himikat123/Big_Clock_BIM32/Solidworks_2023/bed/bed_cover_middle.png

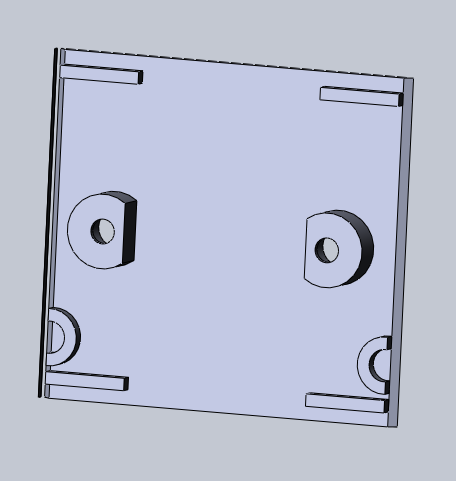
Solidworks_2023/bed/bed_cover_middle.png
