himikat123/Big_Clock_BIM32/Solidworks_2023/buttons/buttons.png

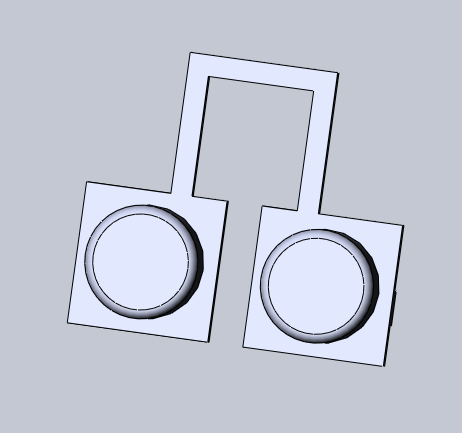
Solidworks_2023/buttons/buttons.png
