himikat123/Big_Clock_BIM32/Solidworks_2023/digit/digit_cover.png

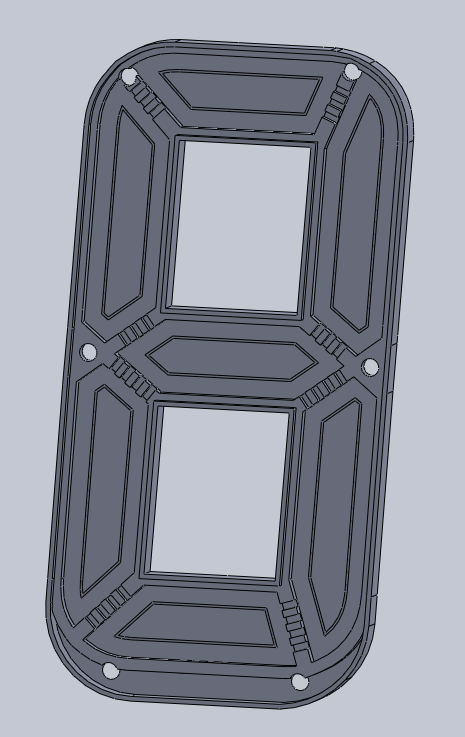
Solidworks_2023/digit/digit_cover.png
