himikat123/Big_Clock_BIM32/Solidworks_2023/digit/digit_frame.png

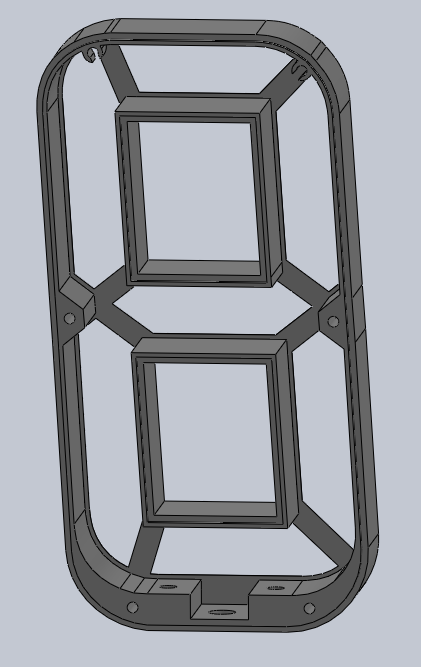
Solidworks_2023/digit/digit_frame.png
