himikat123/Big_Clock_BIM32/Solidworks_2023/jumpers/jumper_2.png

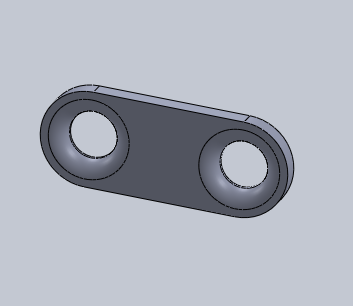
Solidworks_2023/jumpers/jumper_2.png
