himikat123/Big_Clock_BIM32/Solidworks_2023/jumpers/jumper_3.png

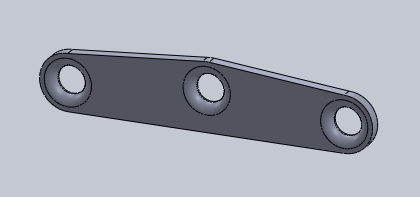
Solidworks_2023/jumpers/jumper_3.png
