himikat123/Big_Clock_BIM32/Solidworks_2023/points/points_diffuser.png

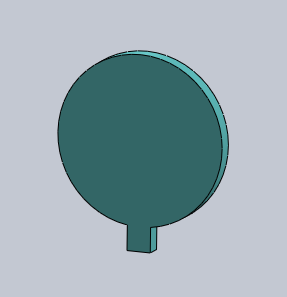
Solidworks_2023/points/points_diffuser.png
