himikat123/Big_Clock_BIM32/Solidworks_2023/points/points_reflector.png

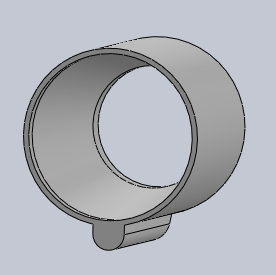
Solidworks_2023/points/points_reflector.png
