himikat123/Big_Clock_BIM32/STL/bed/bed_cover_2.png

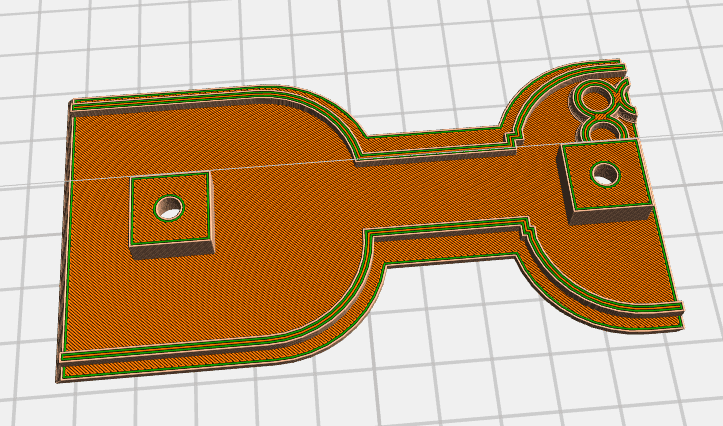
STL/bed/bed_cover_2.png
