himikat123/Big_Clock_BIM32/STL/bed/bed_left.png

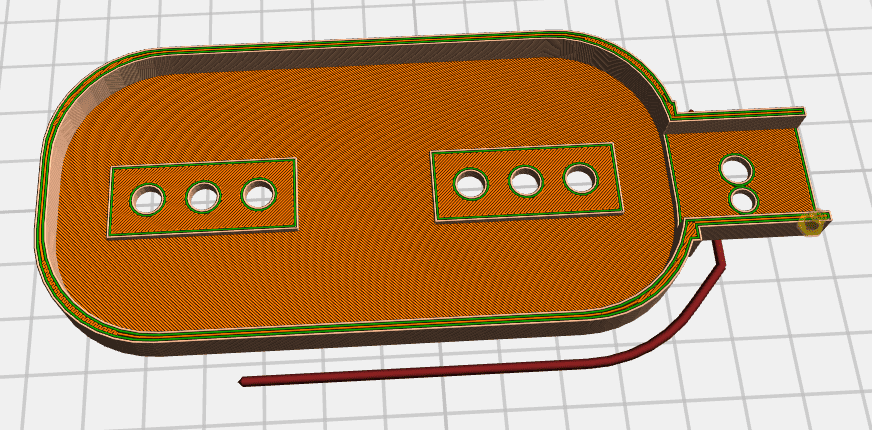
STL/bed/bed_left.png
