himikat123/Big_Clock_BIM32/STL/bed/bed_middle.png

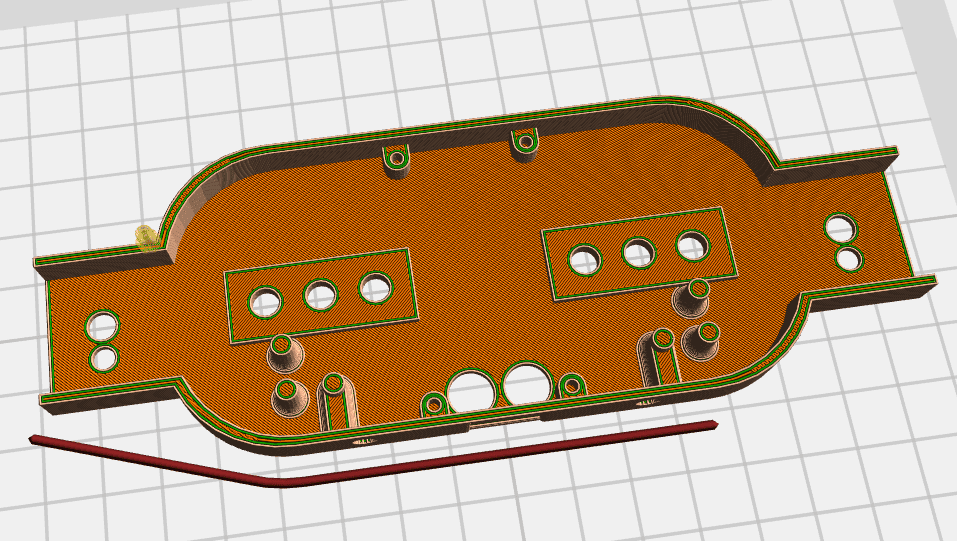
STL/bed/bed_middle.png
