himikat123/Big_Clock_BIM32/STL/bed/bed_right.png

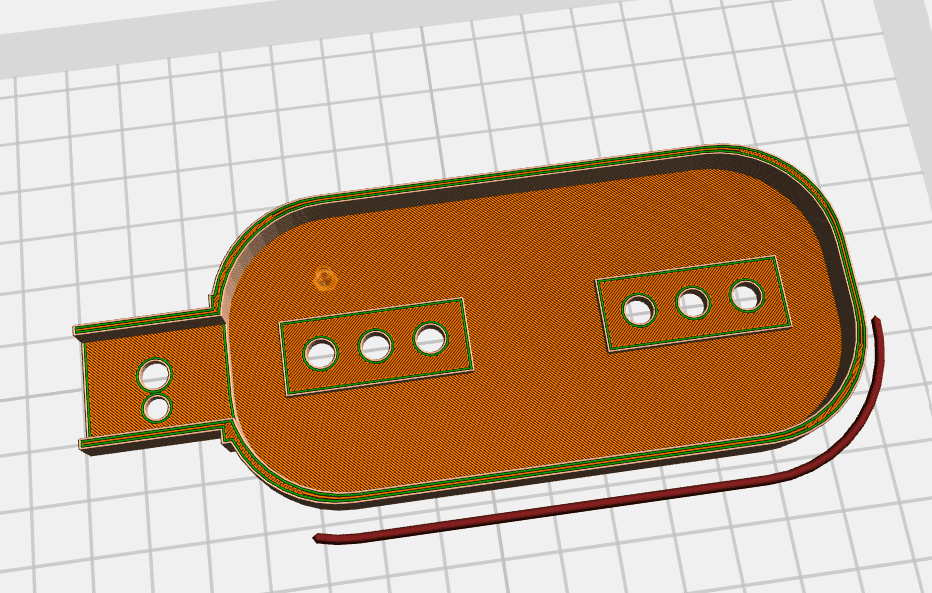
STL/bed/bed_right.png
