himikat123/Big_Clock_BIM32/STL/buttons/buttons.png

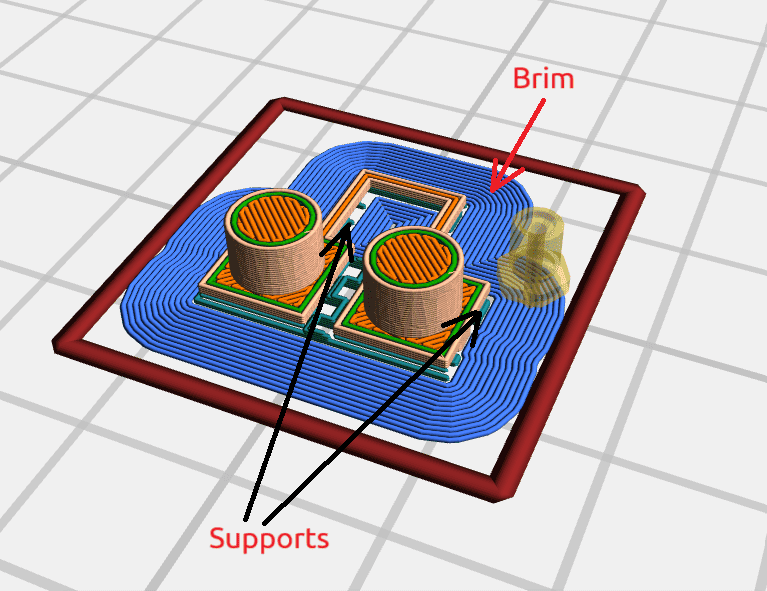
STL/buttons/buttons.png
