himikat123/Big_Clock_BIM32/STL/digit/digit_cover.png

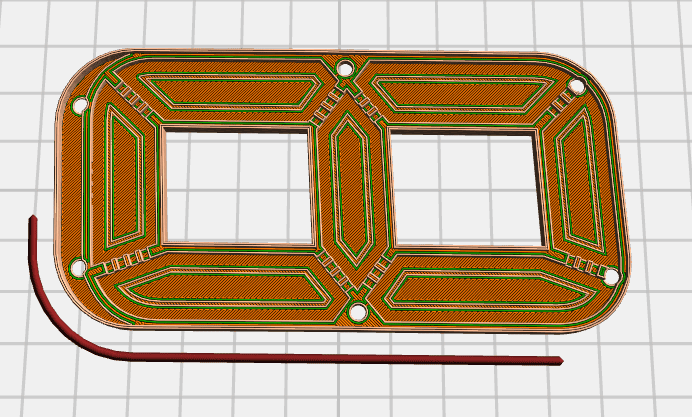
STL/digit/digit_cover.png
