himikat123/Big_Clock_BIM32/STL/digit/digit_diffuser.png

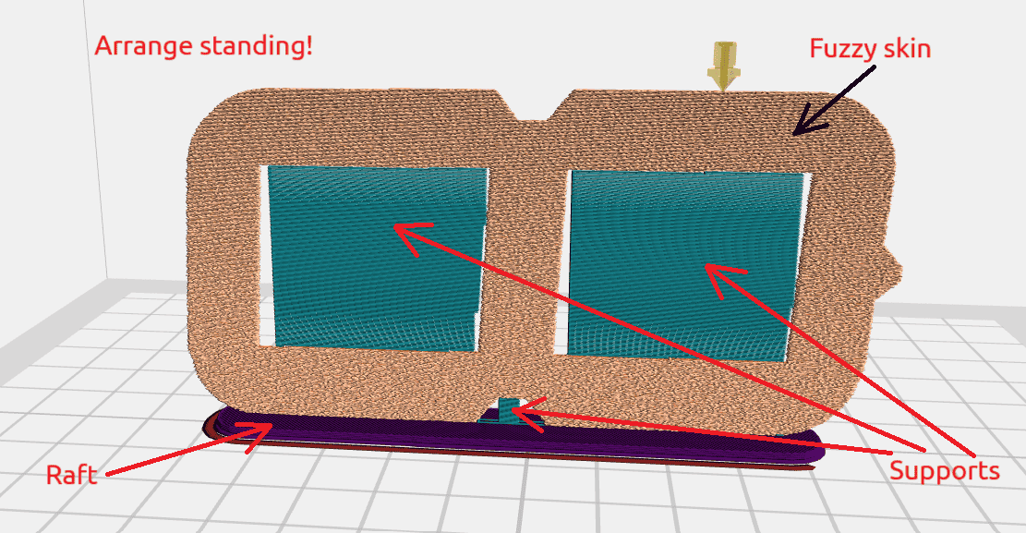
STL/digit/digit_diffuser.png
