himikat123/Big_Clock_BIM32/STL/digit/digit_frame.png

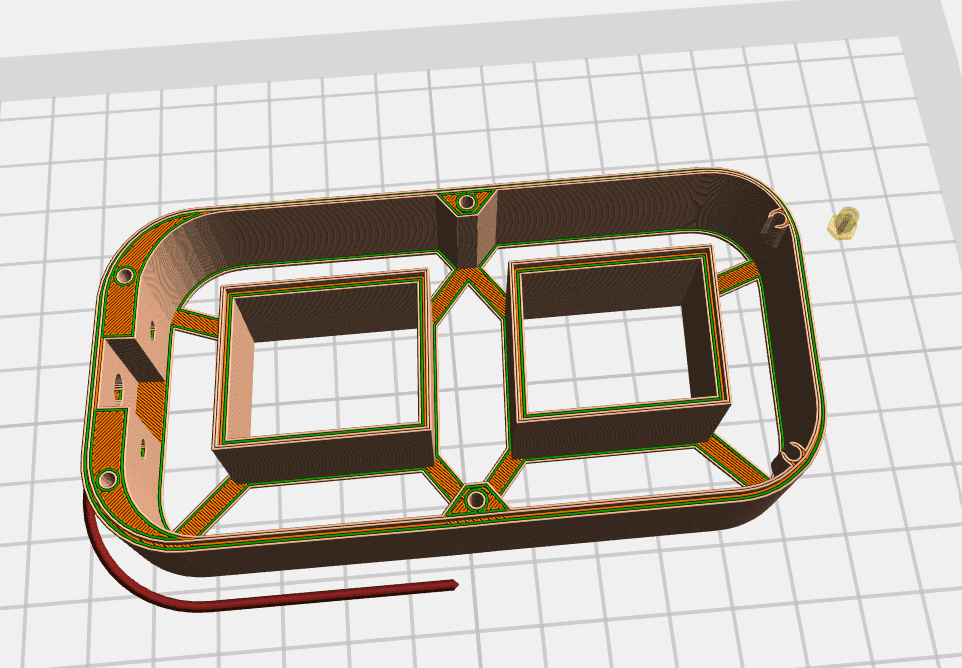
STL/digit/digit_frame.png
