himikat123/Big_Clock_BIM32/STL/digit/digit_reflector.png

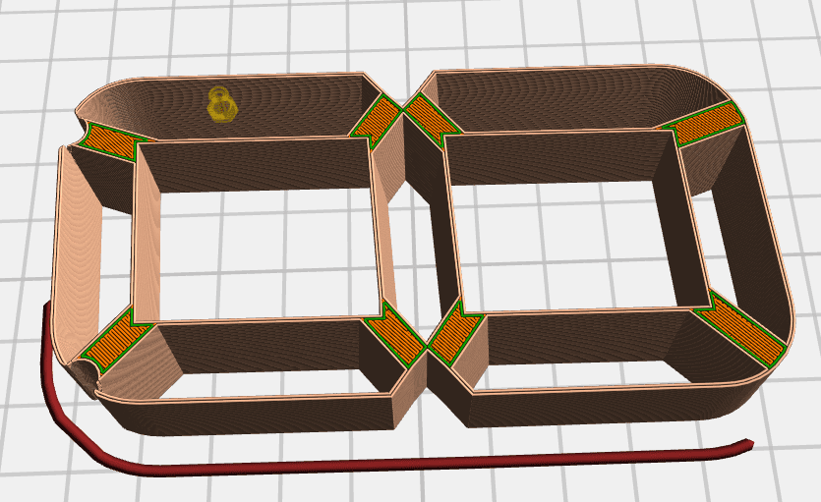
STL/digit/digit_reflector.png
