himikat123/Big_Clock_BIM32/STL/jumpers/jumper_3.png

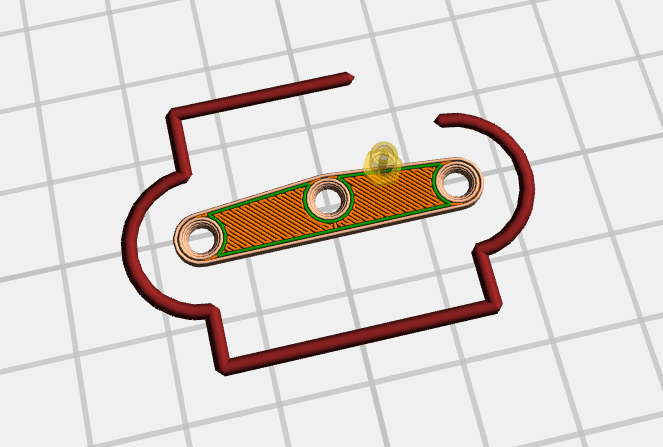
STL/jumpers/jumper_3.png
