himikat123/Big_Clock_BIM32/STL/points/points_cover.png

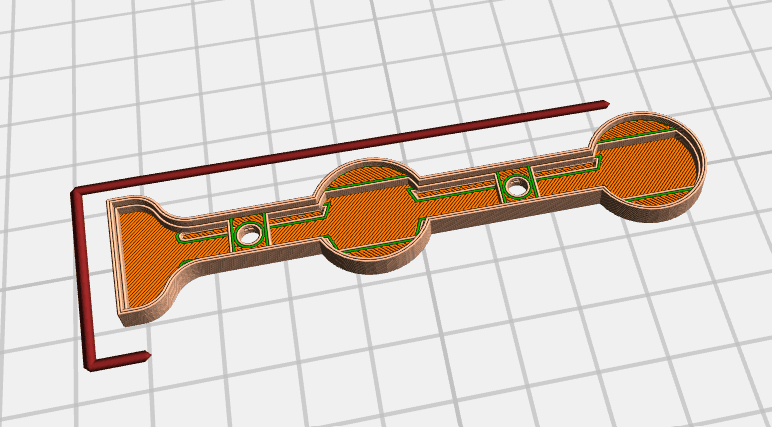
STL/points/points_cover.png
