himikat123/Big_Clock_BIM32/STL/points/points_frame.png

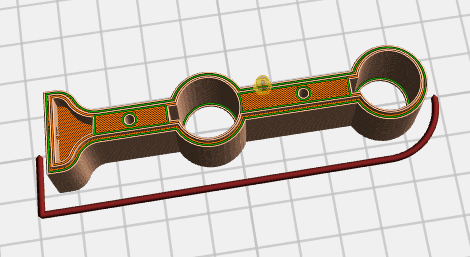
STL/points/points_frame.png
