himikat123/Big_Clock_BIM32/STL/points/points_reflector.png

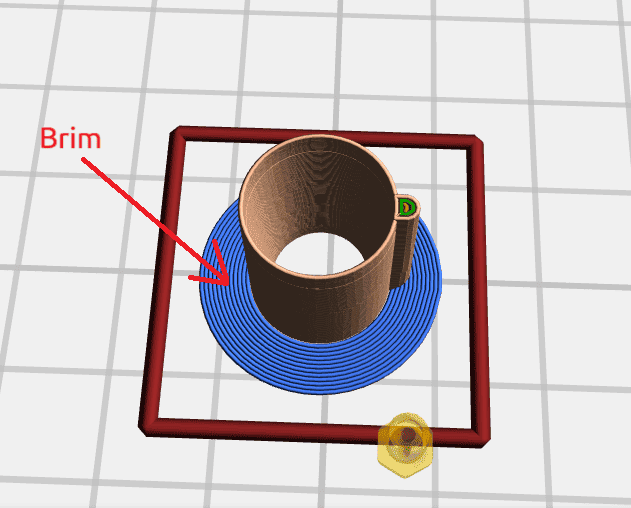
STL/points/points_reflector.png
