himikat123/Big_Clock_BIM32/Solidworks_2023/asssembly.SLDASM

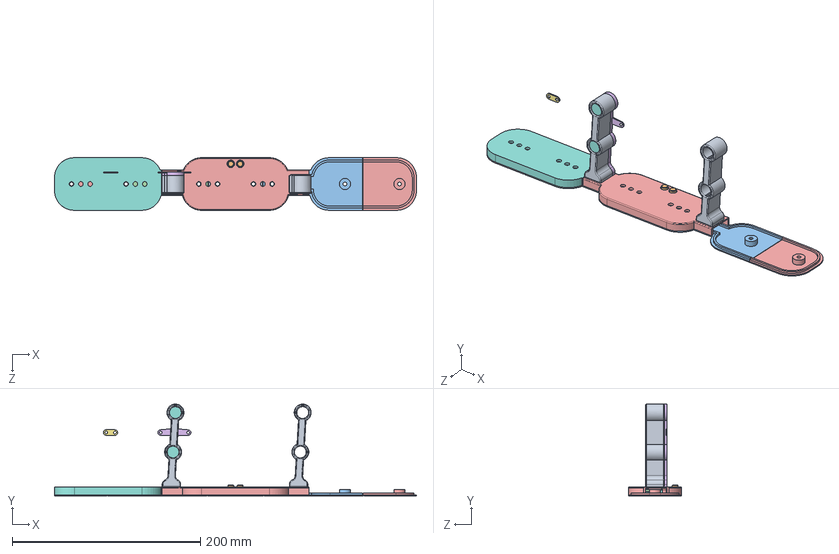
[picture p58: CAD file, 2024-10-17]
Solidworks_2023/asssembly.SLDASM
384.8 x 97.7 x 56.0 mm
points_frame x 2
points_diffuser x 2
points_reflector
points_cover
bed_middle
esp2
btn1 x 2
btn2 x 2
usb
bed_left
jumper_2
jumper_3
bed_cover_edge x 2
bed_cover_2
bed_cover_3
buttons
bed_cover_middle
