himikat123/Big_Clock_BIM32/STL/points/points_reflector.STL

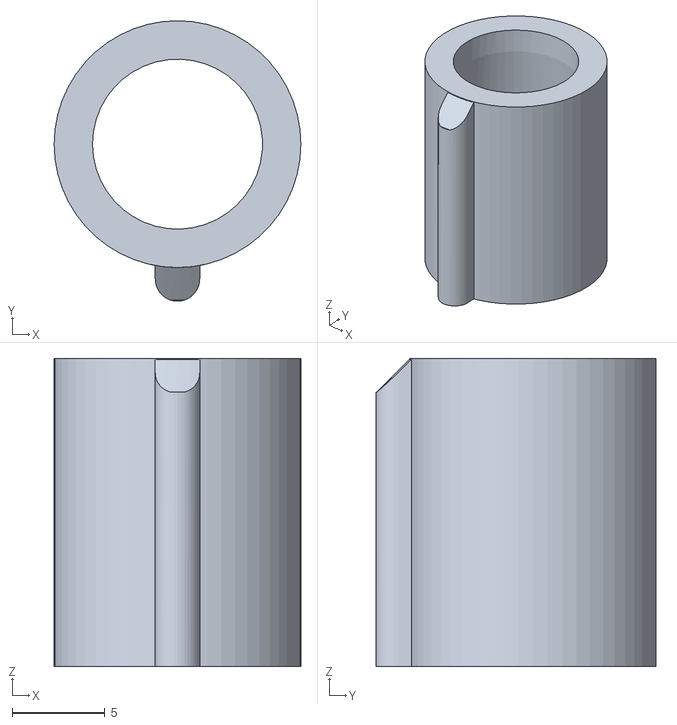
[picture p73: CAD file, 2024-10-17]
STL/points/points_reflector.STL
13.3 x 15.1 x 16.6
