himikat123/Big_Clock_BIM32/Solidworks_2023/bed/bed_cover_middle.SLDPRT

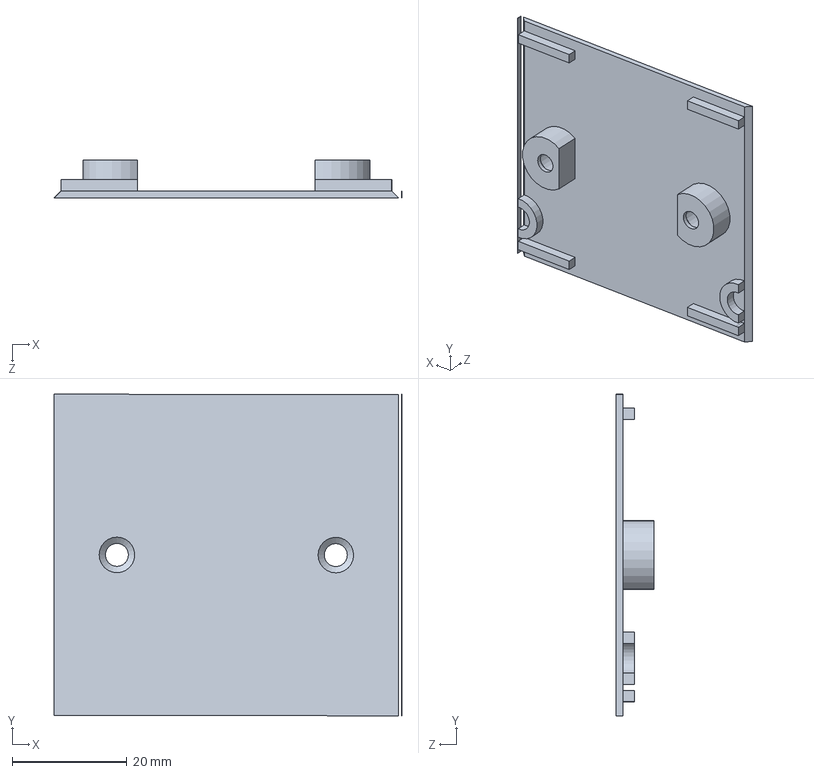
[picture p74: CAD file, 2024-10-17]
Solidworks_2023/bed/bed_cover_middle.SLDPRT
60.6 x 56.0 x 6.60 mm
