himikat123/Big_Clock_BIM32/Solidworks_2023/digit/reflector/G_ref.SLDPRT

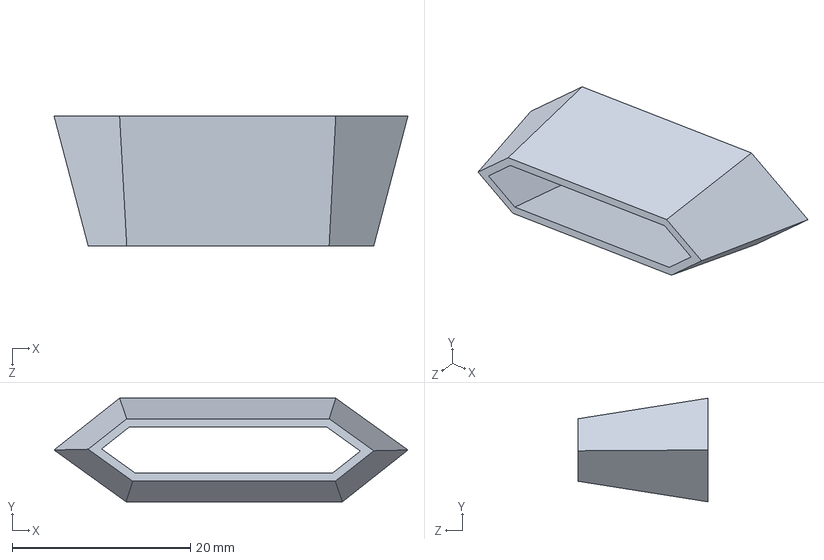
[picture p75: CAD file, 2026-07-15]
Solidworks_2023/digit/reflector/G_ref.SLDPRT
39.7 x 11.6 x 14.6 mm
