himikat123/Big_Clock_BIM32/Solidworks_2023/node mcu/esp2.SLDPRT

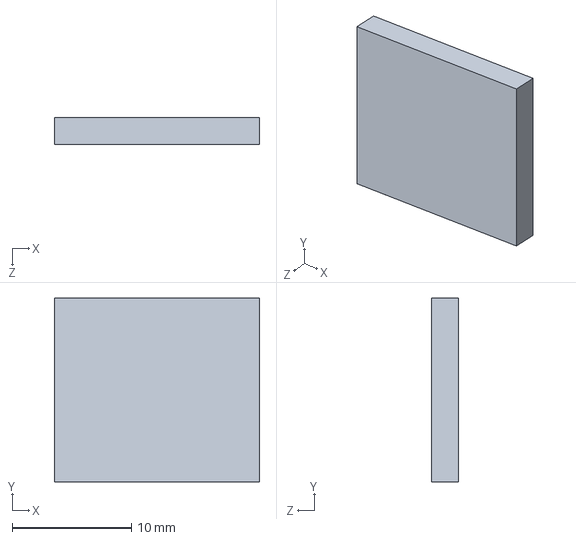
[picture p76: CAD file, 2024-10-17]
Solidworks_2023/node mcu/esp2.SLDPRT
17.2 x 15.4 x 2.30 mm
