himikat123/Big_Clock_BIM32/Solidworks_2023/pcb/pcbPoints.step

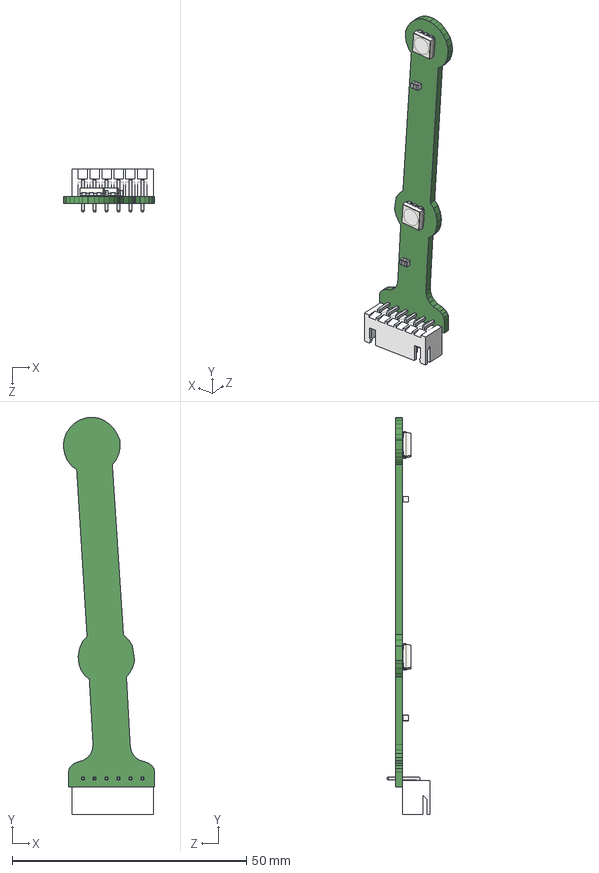
[picture p77: CAD file, 2026-05-27]
Solidworks_2023/pcb/pcbPoints.step
19.5 x 84.7 x 9.22 mm
Board_pcbPoints
0805B104M500NT x 2
led_plcc6_5050_metric x 2
JST_-_XH_-_Thru_(R)_-_6Pin_-_2.54mm
