himikat123/Big_Clock_BIM32/Solidworks_2023/points/points_diffuser.SLDPRT

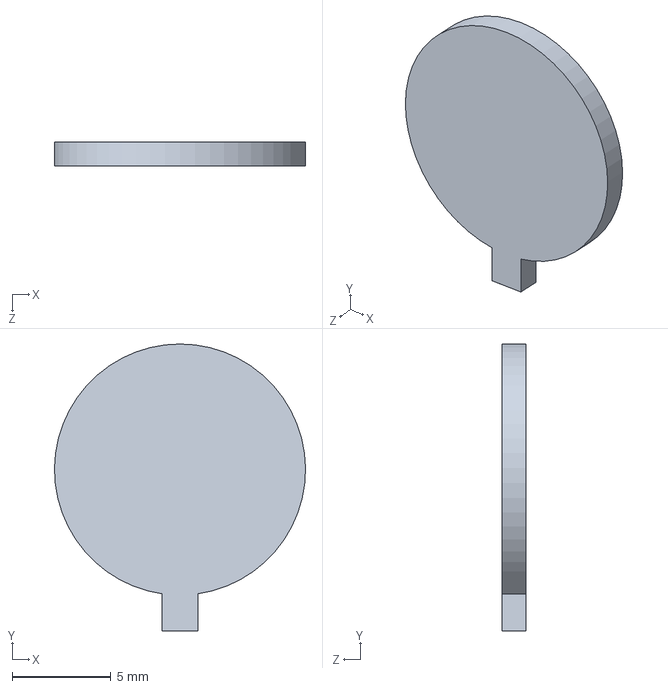
[picture p78: CAD file, 2024-10-17]
Solidworks_2023/points/points_diffuser.SLDPRT
12.7 x 14.5 x 1.20 mm
