himikat123/Big_Clock_BIM32/STL/bed/bed_cover_2.STL

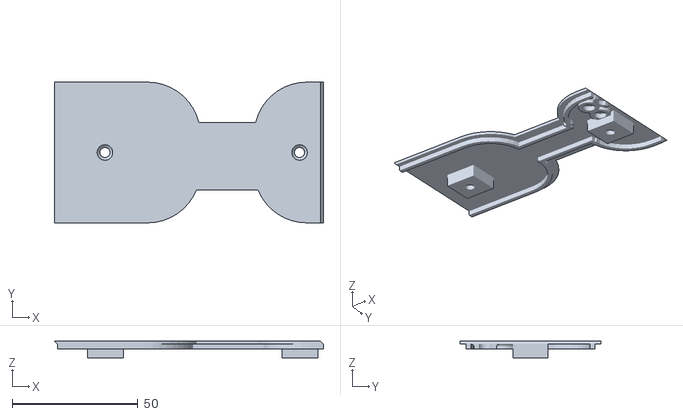
[picture p79: CAD file, 2024-10-17]
STL/bed/bed_cover_2.STL
107.0 x 56.0 x 6.60
