himikat123/Big_Clock_BIM32/STL/digit/diffuser/E.STL

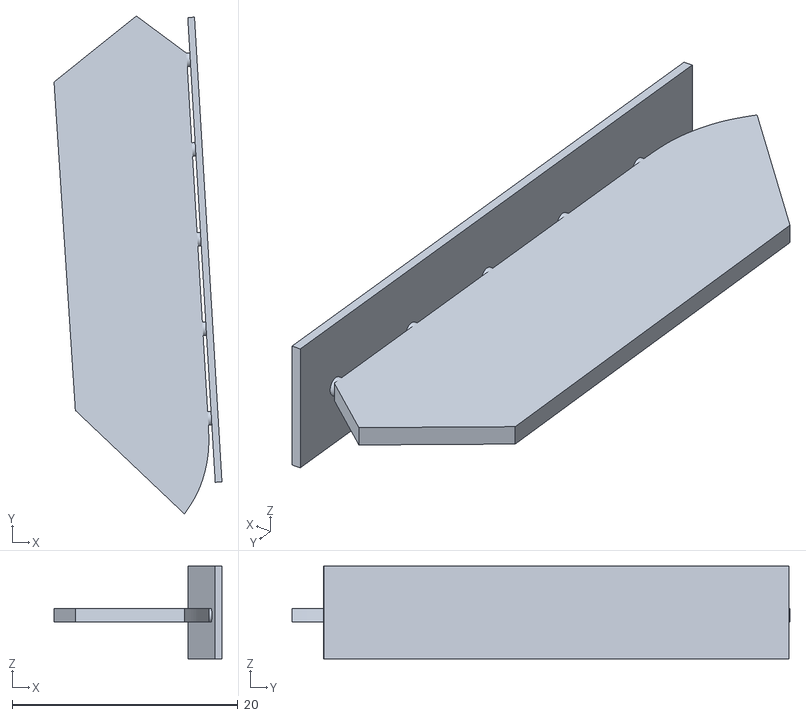
[picture p80: CAD file, 2026-07-06]
STL/digit/diffuser/E.STL
14.9 x 44.1 x 8.21
