himikat123/Big_Clock_BIM32/STL/digit/digit_frame.STL

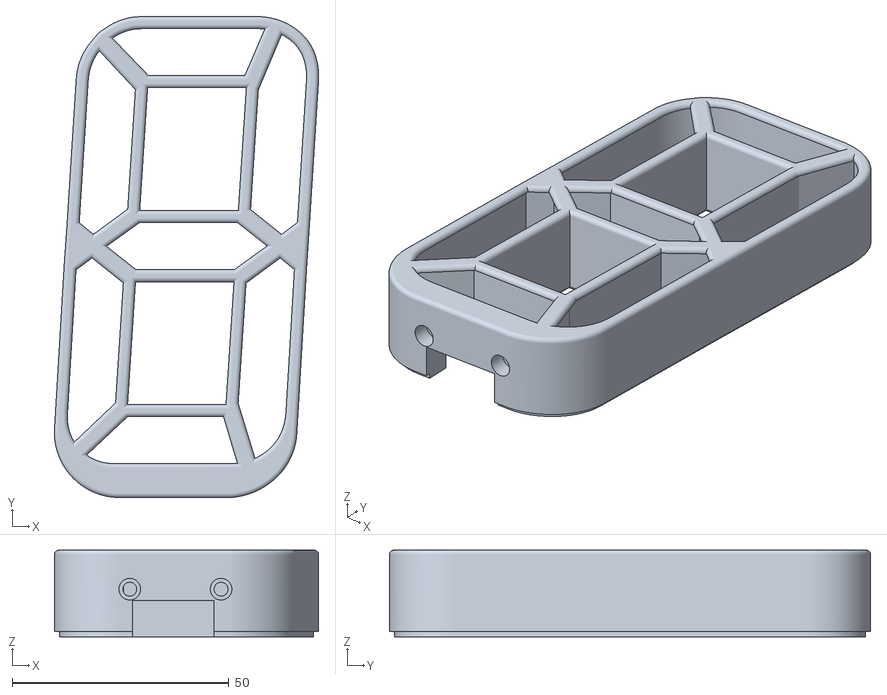
[picture p81: CAD file, 2026-07-06]
STL/digit/digit_frame.STL
61.0 x 111.0 x 20.0
