himikat123/Big_Clock_BIM32/STL/digit/reflector/C_ref.STL

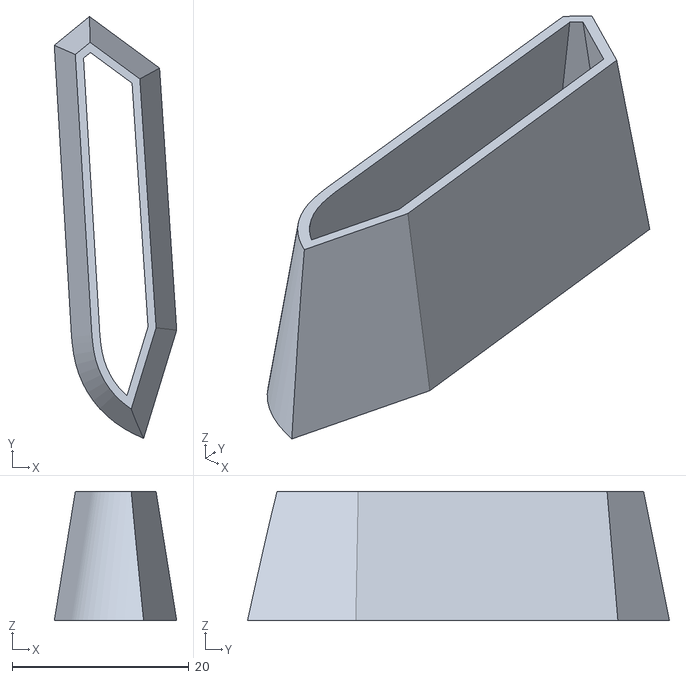
[picture p82: CAD file, 2026-07-15]
STL/digit/reflector/C_ref.STL
13.8 x 47.7 x 14.6
