himikat123/Big_Clock_BIM32/STL/points/points_cover.STL

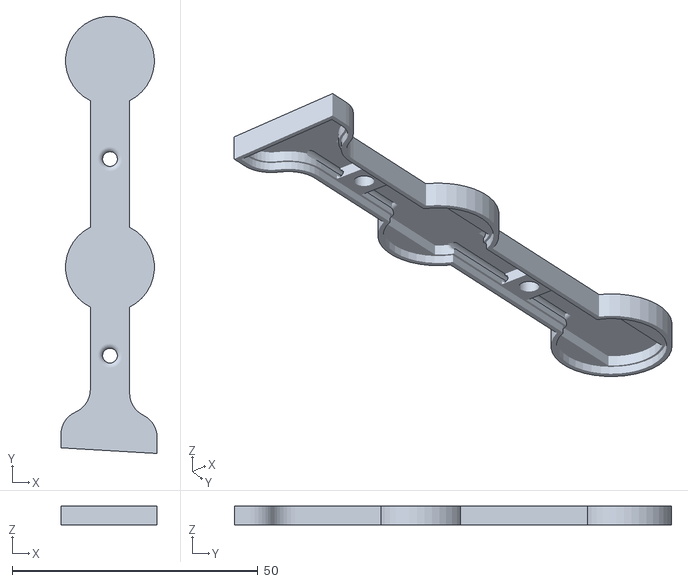
[picture p83: CAD file, 2024-10-17]
STL/points/points_cover.STL
19.6 x 88.9 x 3.80
