himikat123/Big_Clock_BIM32/Solidworks_2023/digit/diffuser/C.SLDPRT

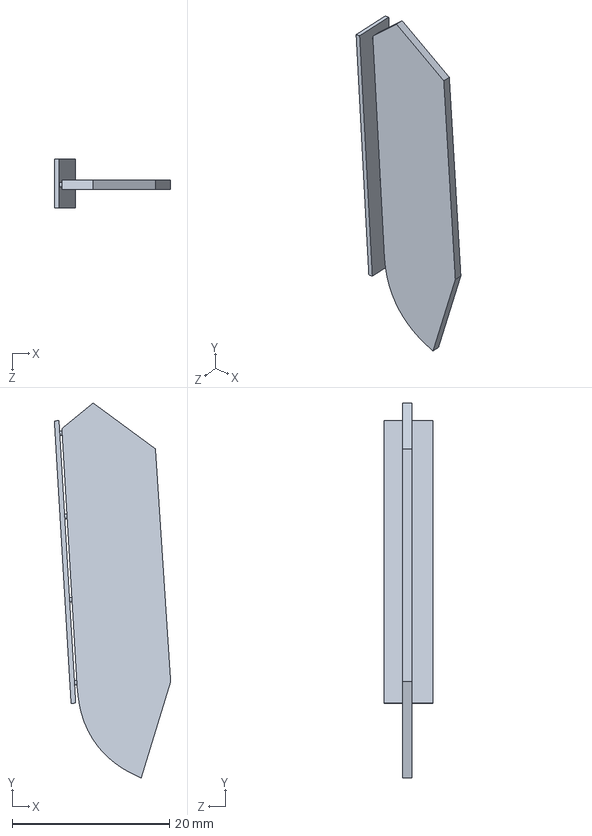
[picture p84: CAD file, 2026-07-15]
Solidworks_2023/digit/diffuser/C.SLDPRT
14.8 x 47.7 x 6.24 mm
