himikat123/Big_Clock_BIM32/Solidworks_2023/node mcu/btn2.SLDPRT

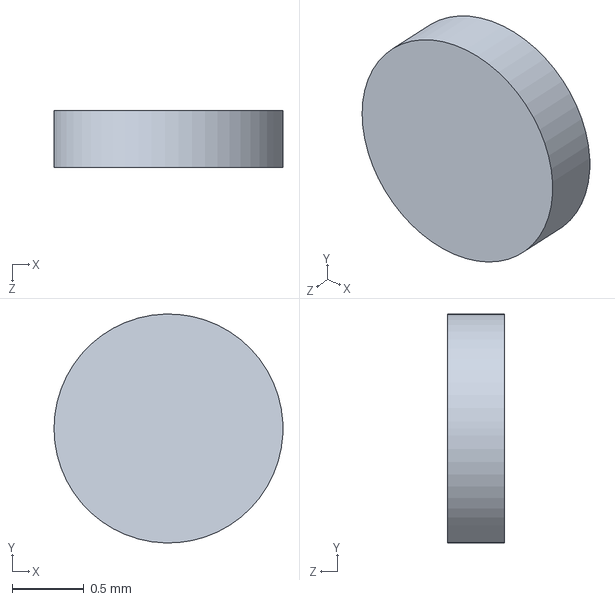
[picture p85: CAD file, 2024-10-17]
Solidworks_2023/node mcu/btn2.SLDPRT
1.60 x 1.60 x 0.4 mm
