himikat123/Big_Clock_BIM32/Solidworks_2023/pcb/pcbDigit.step

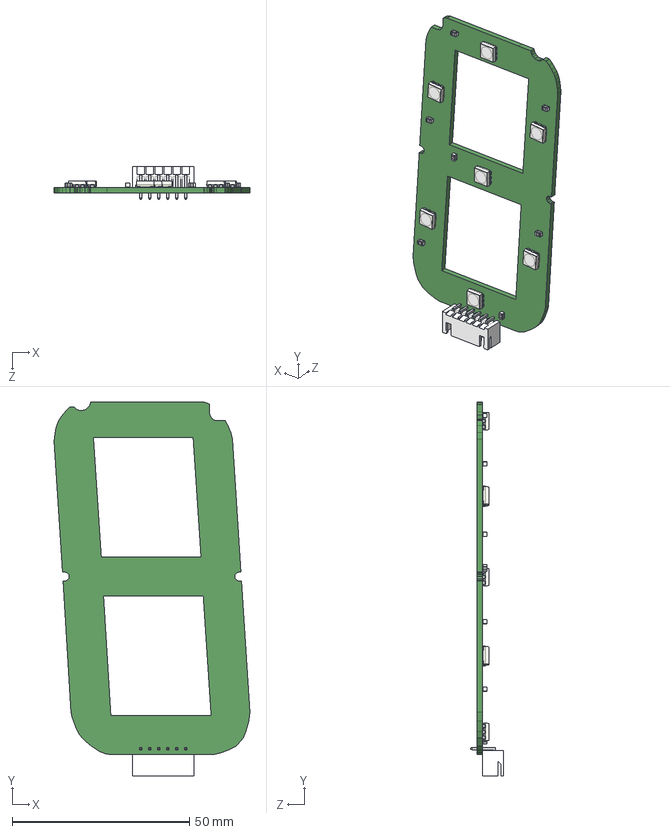
[picture p86: CAD file, 2026-05-27]
Solidworks_2023/pcb/pcbDigit.step
55.2 x 105.5 x 9.22 mm
Board_pcbDigit
0805B104M500NT x 7
led_plcc6_5050_metric x 7
JST_-_XH_-_Thru_(R)_-_6Pin_-_2.54mm
