himikat123/Big_Clock_BIM32/STL/bed/bed_middle.STL

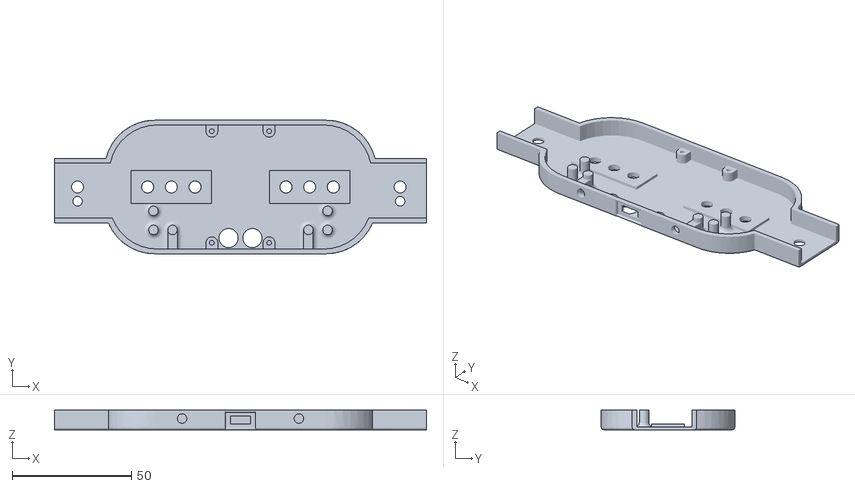
[picture p87: CAD file, 2024-10-17]
STL/bed/bed_middle.STL
156.0 x 56.0 x 8.20
