himikat123/Big_Clock_BIM32/STL/digit/diffuser/G.STL

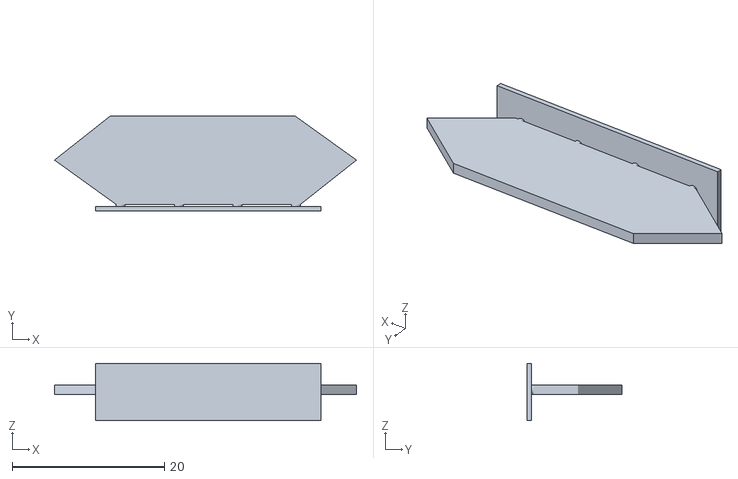
[picture p88: CAD file, 2026-07-06]
STL/digit/diffuser/G.STL
39.7 x 12.5 x 7.52
