himikat123/Big_Clock_BIM32/STL/digit/digit_reflector.STL

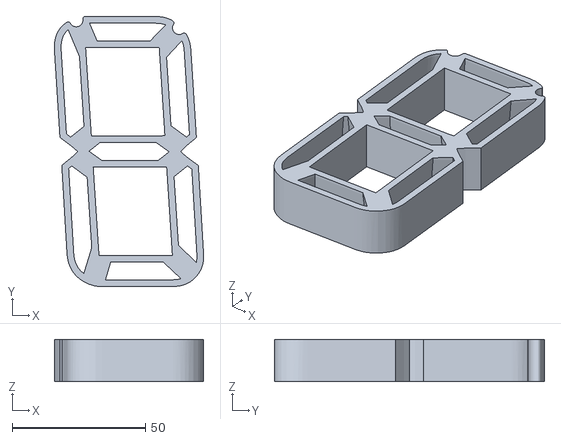
[picture p89: CAD file, 2024-10-17]
STL/digit/digit_reflector.STL
55.9 x 101.2 x 15.8
