himikat123/Big_Clock_BIM32/Solidworks_2023/node mcu/pin.SLDPRT

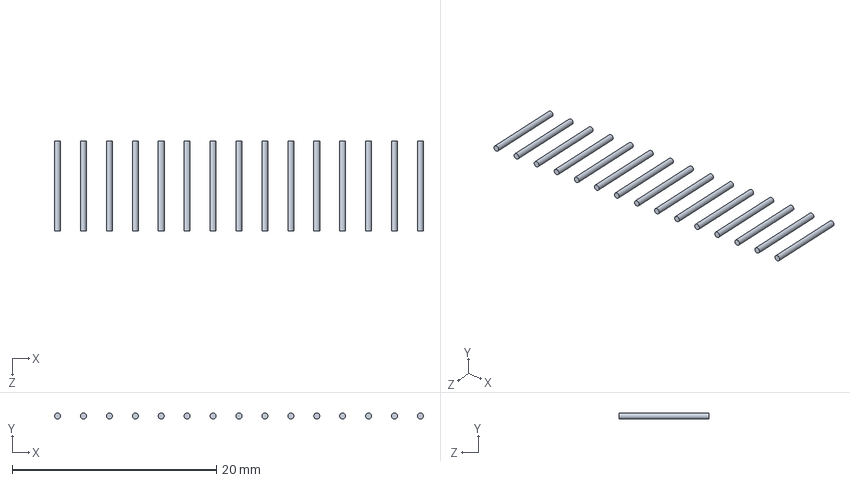
[picture p90: CAD file, 2024-10-17]
Solidworks_2023/node mcu/pin.SLDPRT
36.2 x 0.6 x 8.80 mm
