himikat123/Big_Clock_BIM32/STL/digit/diffuser/A.STL

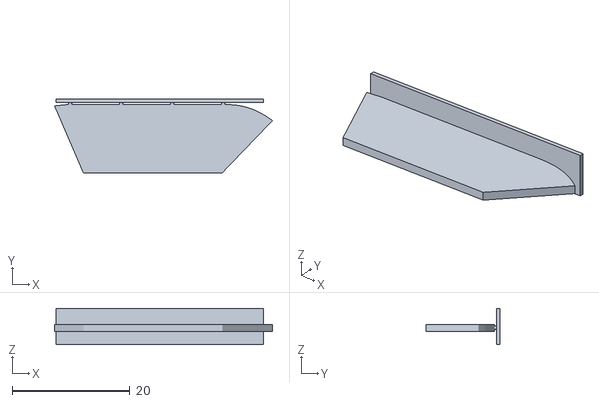
[picture p91: CAD file, 2026-07-06]
STL/digit/diffuser/A.STL
37.1 x 12.5 x 6.20
