himikat123/Big_Clock_BIM32/STL/digit/digit_diffuser.STL

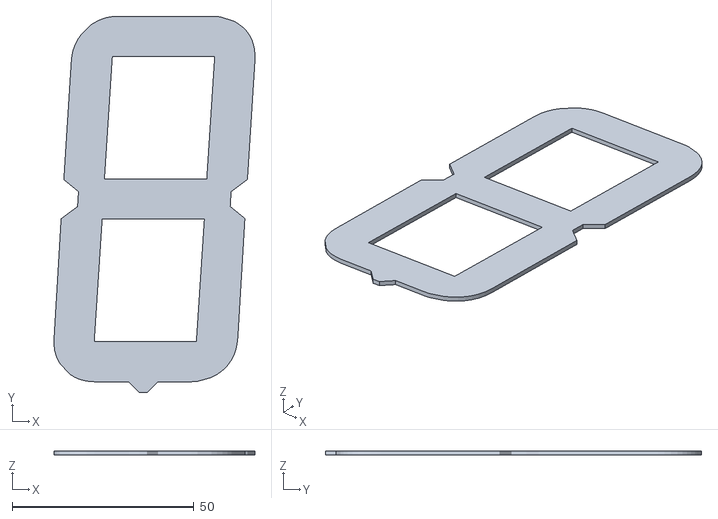
[picture p92: CAD file, 2024-10-17]
STL/digit/digit_diffuser.STL
55.3 x 103.6 x 1.20
