himikat123/Big_Clock_BIM32/Solidworks_2023/node mcu/btn1.SLDPRT

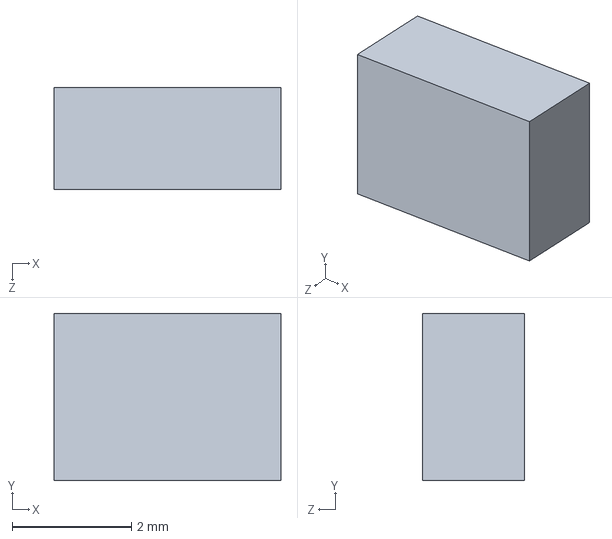
[picture p93: CAD file, 2024-10-17]
Solidworks_2023/node mcu/btn1.SLDPRT
3.80 x 2.80 x 1.70 mm
