himikat123/Big_Clock_BIM32/STL/bed/bed_cover_edge.STL

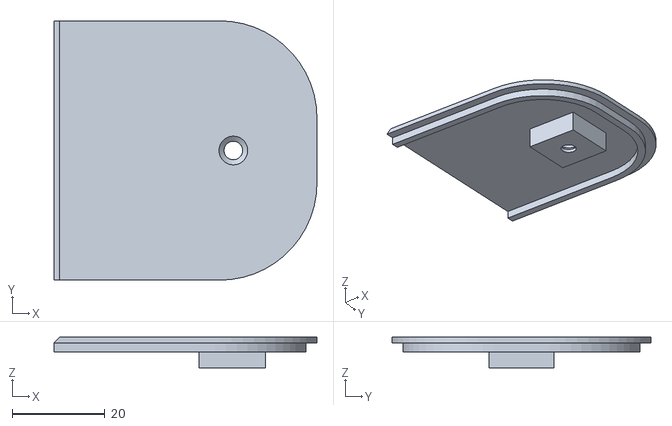
[picture p94: CAD file, 2024-10-17]
STL/bed/bed_cover_edge.STL
56.8 x 56.0 x 6.60
