himikat123/Big_Clock_BIM32/Solidworks_2023/bed/bed_frame.SLDPRT

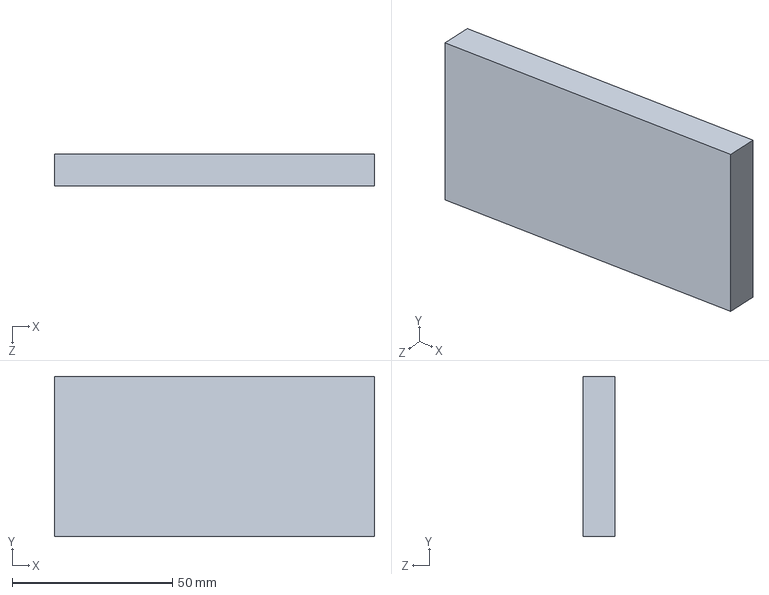
[picture p95: CAD file, 2024-10-17]
Solidworks_2023/bed/bed_frame.SLDPRT
100.0 x 50.0 x 10.0 mm
