himikat123/Big_Clock_BIM32/Solidworks_2023/digit/diffuser/B.SLDPRT

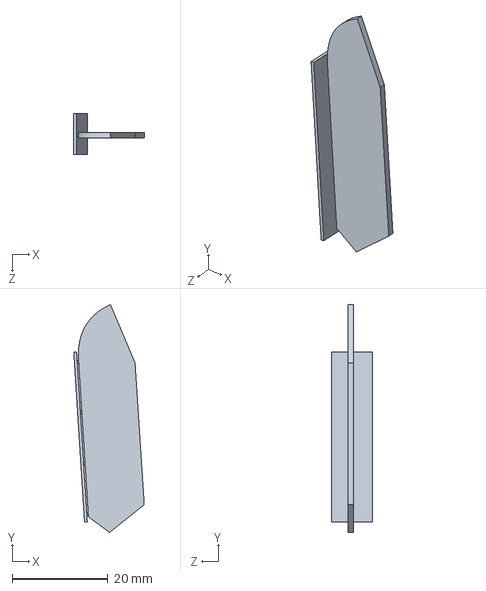
[picture p96: CAD file, 2026-07-13]
Solidworks_2023/digit/diffuser/B.SLDPRT
14.7 x 47.6 x 8.57 mm
