himikat123/Big_Clock_BIM32/Solidworks_2023/digit/reflector/A_ref.SLDPRT

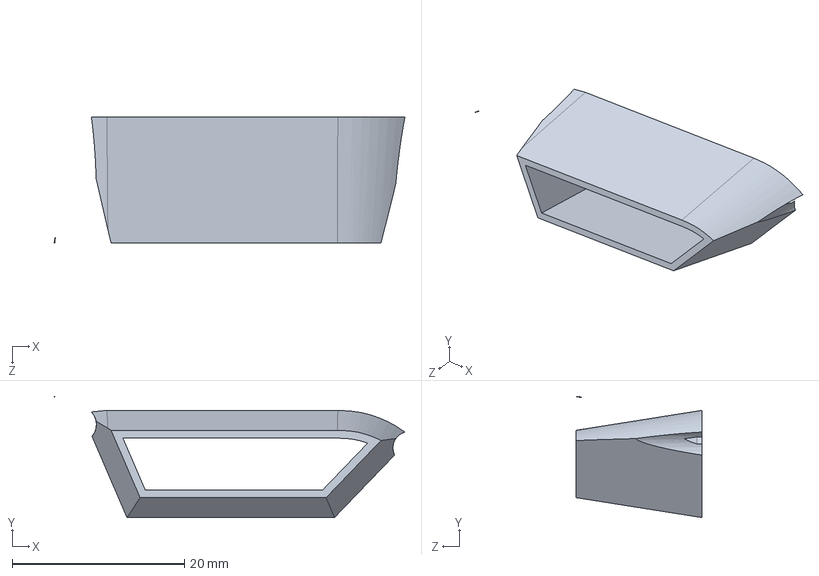
[picture p97: CAD file, 2026-07-14]
Solidworks_2023/digit/reflector/A_ref.SLDPRT
40.7 x 14.1 x 14.6 mm
