himikat123/Big_Clock_BIM32/Solidworks_2023/node mcu/usb.SLDPRT

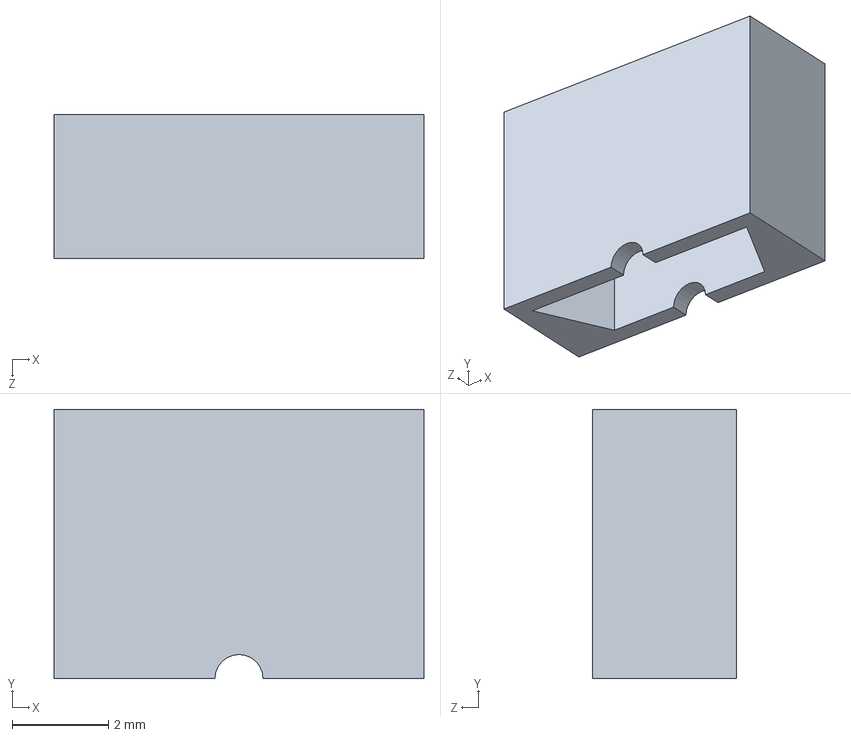
[picture p98: CAD file, 2024-10-17]
Solidworks_2023/node mcu/usb.SLDPRT
7.70 x 5.60 x 3.00 mm
