himikat123/Big_Clock_BIM32/Solidworks_2023/node mcu/pcb.SLDPRT

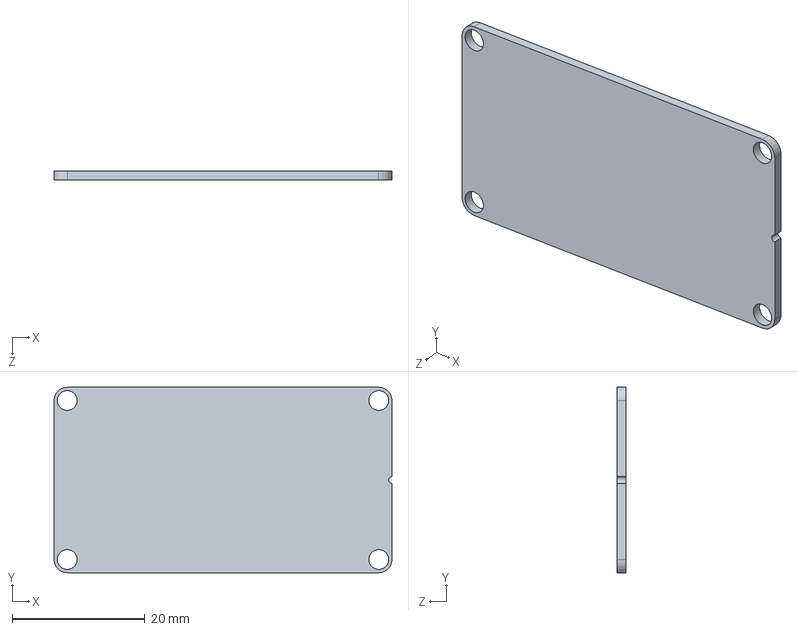
[picture p99: CAD file, 2024-10-17]
Solidworks_2023/node mcu/pcb.SLDPRT
51.0 x 28.0 x 1.30 mm
