himikat123/Big_Clock_BIM32/Solidworks_2023/node mcu/dip.SLDPRT

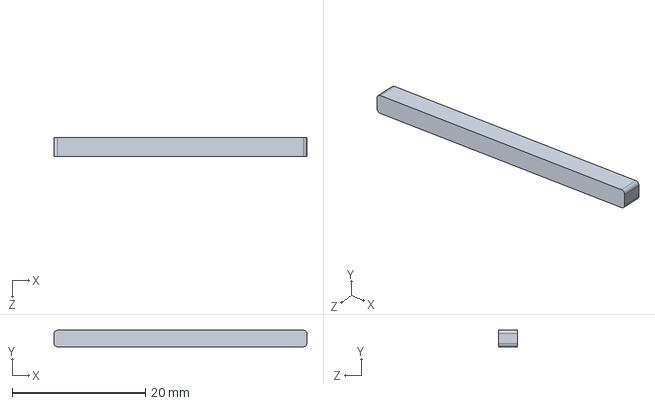
[picture p100: CAD file, 2024-10-17]
Solidworks_2023/node mcu/dip.SLDPRT
38.0 x 2.50 x 2.80 mm
