himikat123/Big_Clock_BIM32/Solidworks_2023/node mcu/esp1.SLDPRT

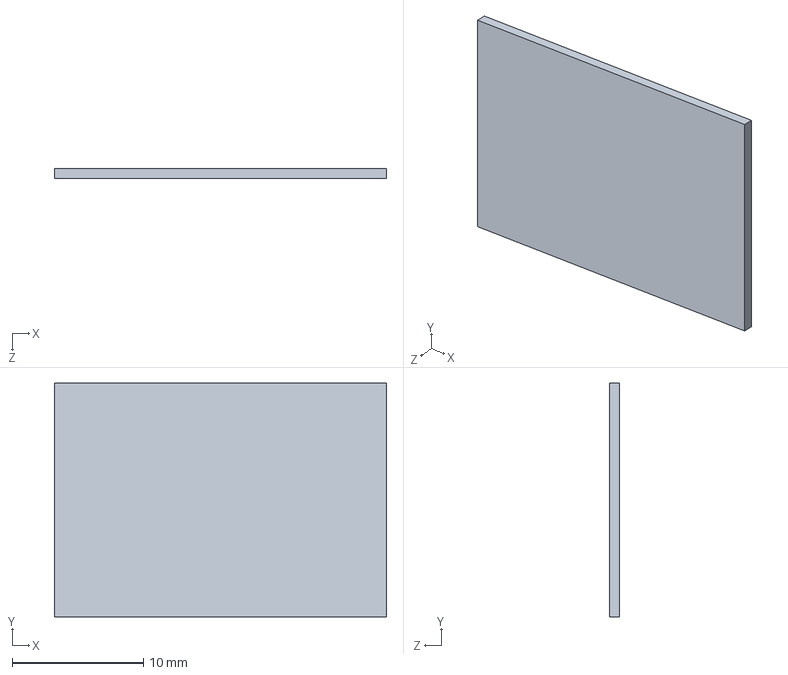
[picture p101: CAD file, 2024-10-17]
Solidworks_2023/node mcu/esp1.SLDPRT
25.3 x 17.8 x 0.8 mm
