himikat123/Big_Clock_BIM32/Solidworks_2023/digit/digit.SLDASM

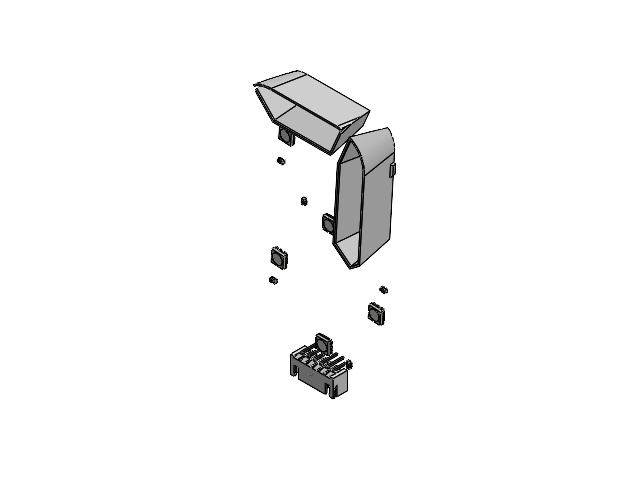
[picture p102: CAD file, 2026-07-13]
Solidworks_2023/digit/digit.SLDASM
0805B104M500NT_1.step x 7
led_plcc6_5050_metric_1.step x 7
JST_-_XH_-_Thru_(R)_-_6Pin_-_2.54mm_1.step
A_ref
B_ref
